jshorstman/Analog-XY-Plotter-Output-to-HPGL-Translator/Photos/IMG_0013.JPG

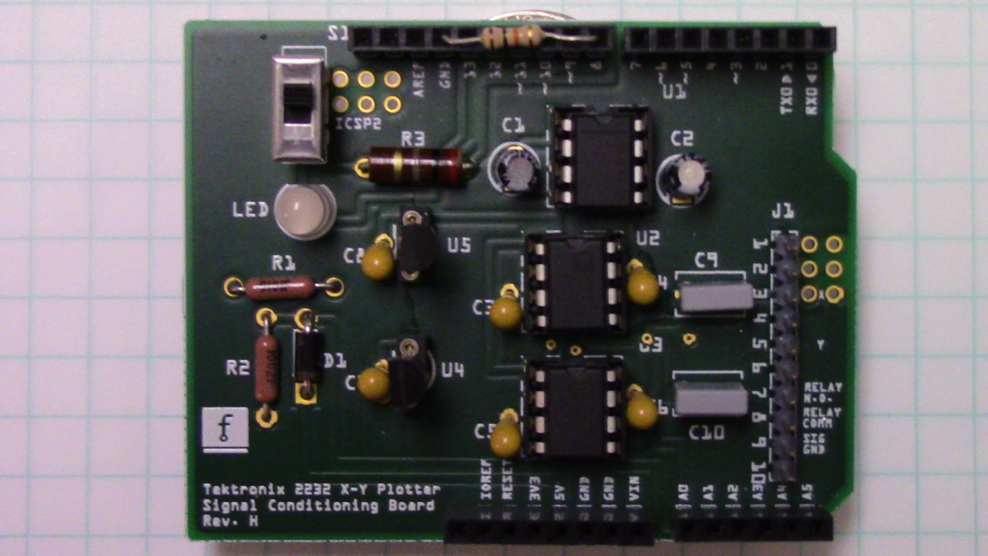
Photos/IMG_0013.JPG
