jshorstman/Analog-XY-Plotter-Output-to-HPGL-Translator/Photos/IMG_0014.JPG

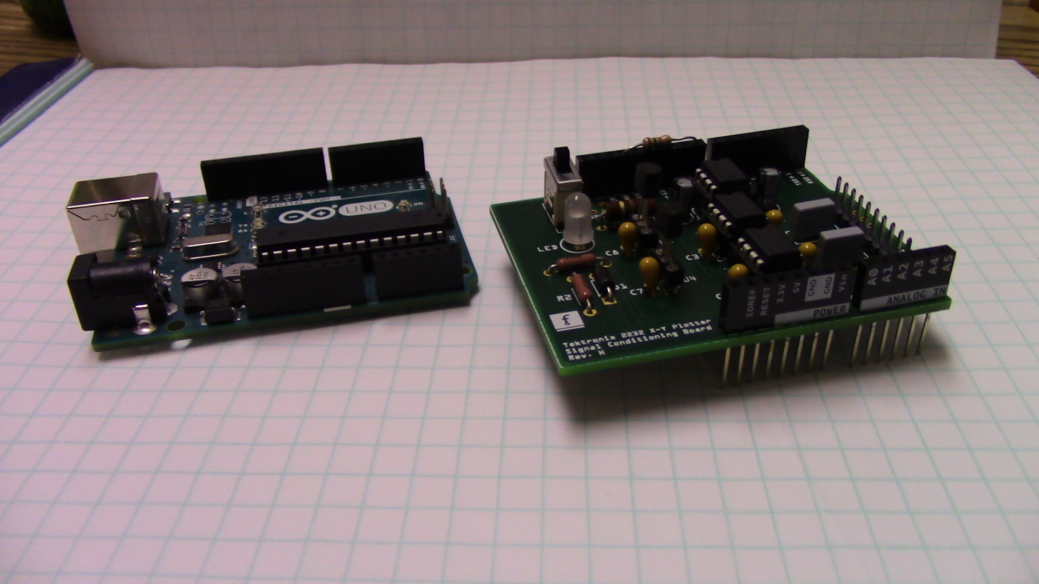
Photos/IMG_0014.JPG
