jshorstman/Analog-XY-Plotter-Output-to-HPGL-Translator/Photos/IMG_0081.JPG

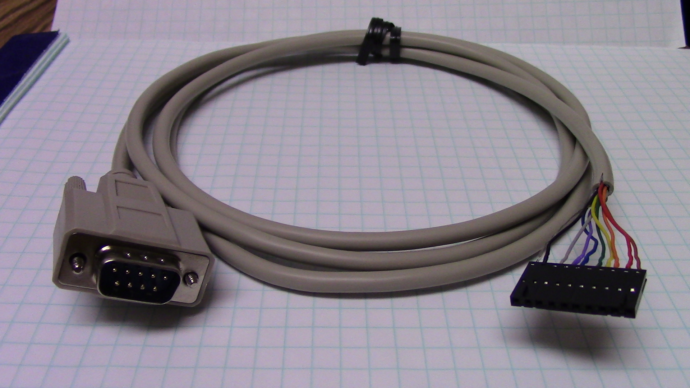
Photos/IMG_0081.JPG
