jshorstman/Analog-XY-Plotter-Output-to-HPGL-Translator/Photos/IMG_0082.JPG

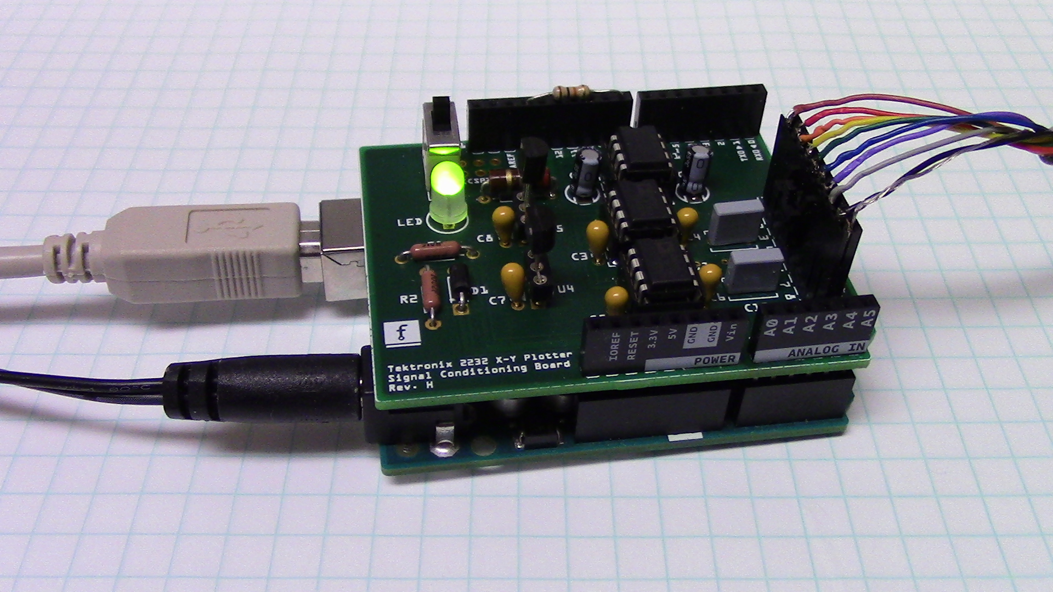
Photos/IMG_0082.JPG
